ProjInt2/deltarobot/datasheets/l298n-module/Motor Driver Module-L298N - Wiki_arquivos/Motor1.JPG

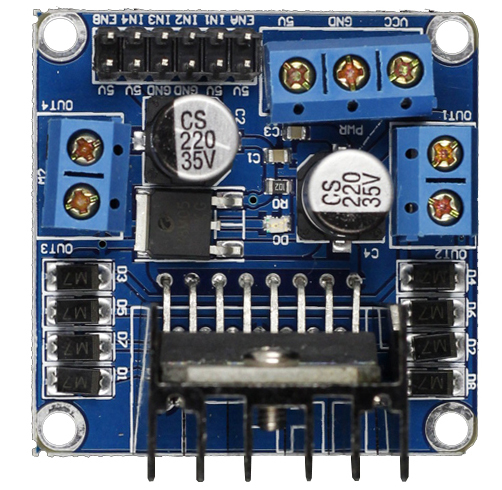
datasheets/l298n-module/Motor Driver Module-L298N - Wiki_arquivos/Motor1.JPG
