ProjInt2/deltarobot/datasheets/l298n-module/Motor Driver Module-L298N - Wiki_arquivos/Motor6.png

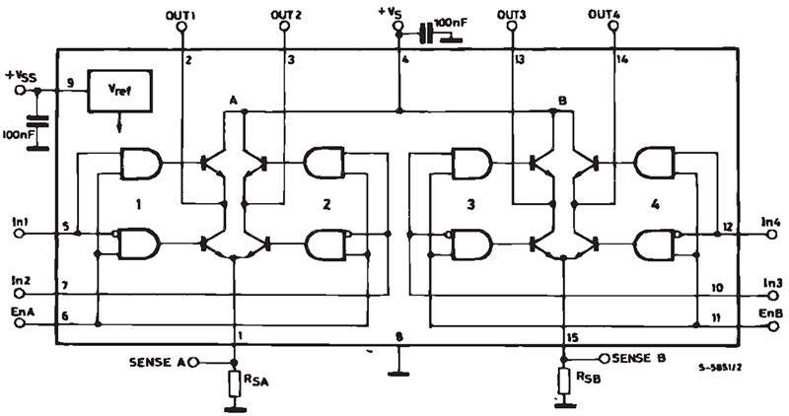
datasheets/l298n-module/Motor Driver Module-L298N - Wiki_arquivos/Motor6.png
