ProjInt2/deltarobot/sw/deltarobot-gui/res/3d-mock.png

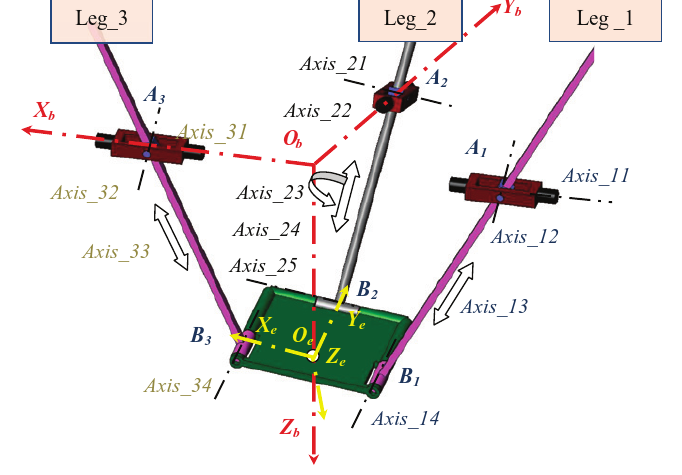
sw/deltarobot-gui/res/3d-mock.png
