ProjInt2/deltarobot/sw/deltarobot-gui/res/ed-mock-2.png

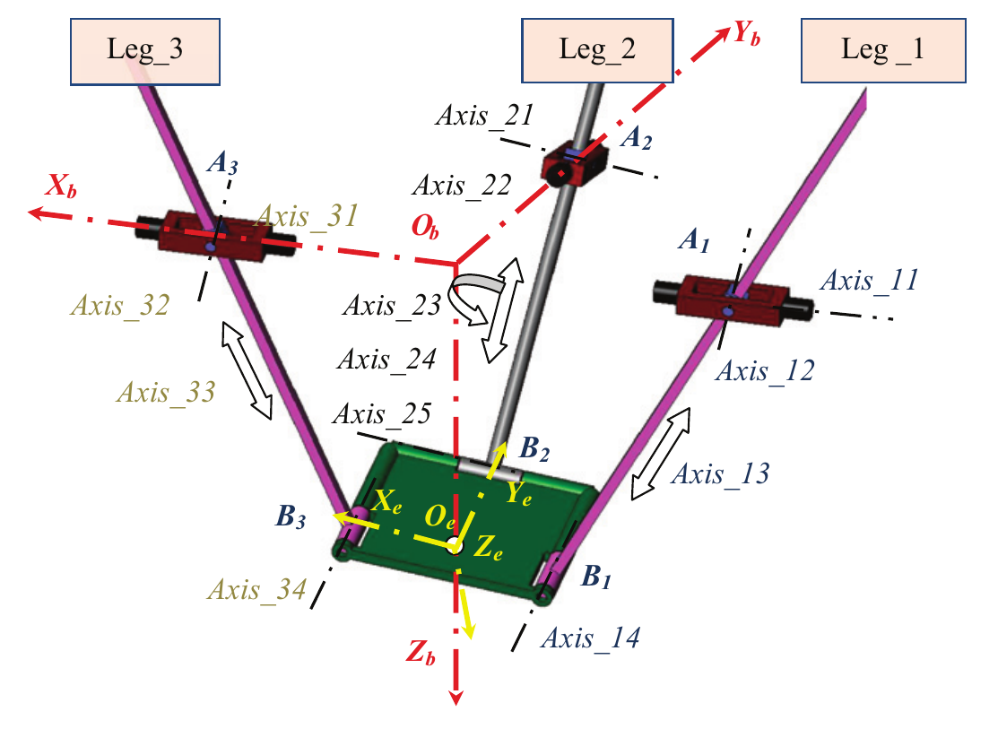
sw/deltarobot-gui/res/ed-mock-2.png
